visrealm/pico-56/episodes/ep01-vga/ep01-vga-04-boing/res/background.png

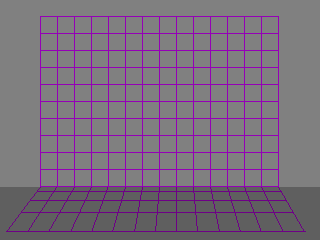
episodes/ep01-vga/ep01-vga-04-boing/res/background.png
