visrealm/pico-56/episodes/ep01-vga/ep01-vga-08b-image-800/res/birds.png

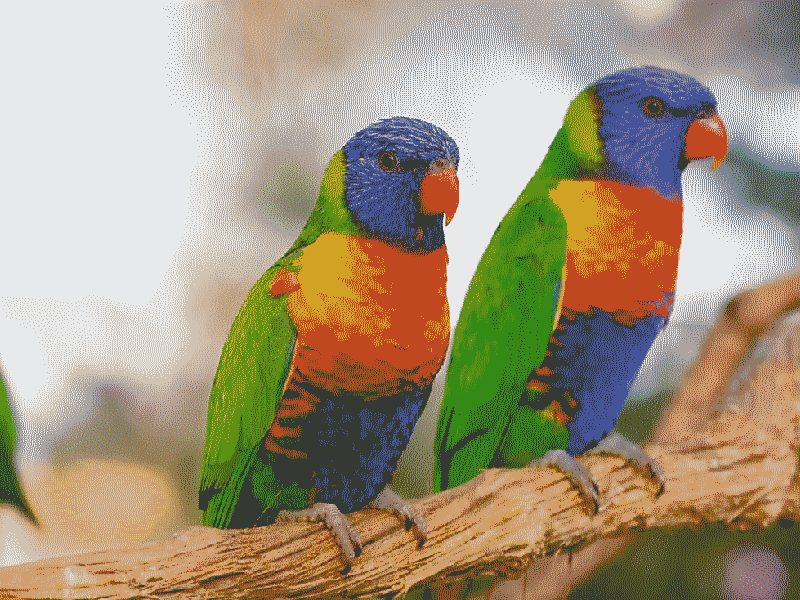
episodes/ep01-vga/ep01-vga-08b-image-800/res/birds.png
