visrealm/pico-56/episodes/ep01-vga/ep01-vga-09-slideshow/res/toucan.png

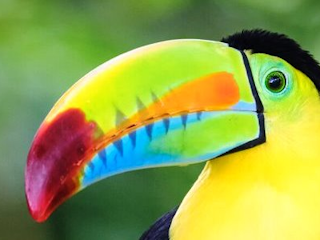
episodes/ep01-vga/ep01-vga-09-slideshow/res/toucan.png
