visrealm/pico-56/img/breadboard_1.jpg

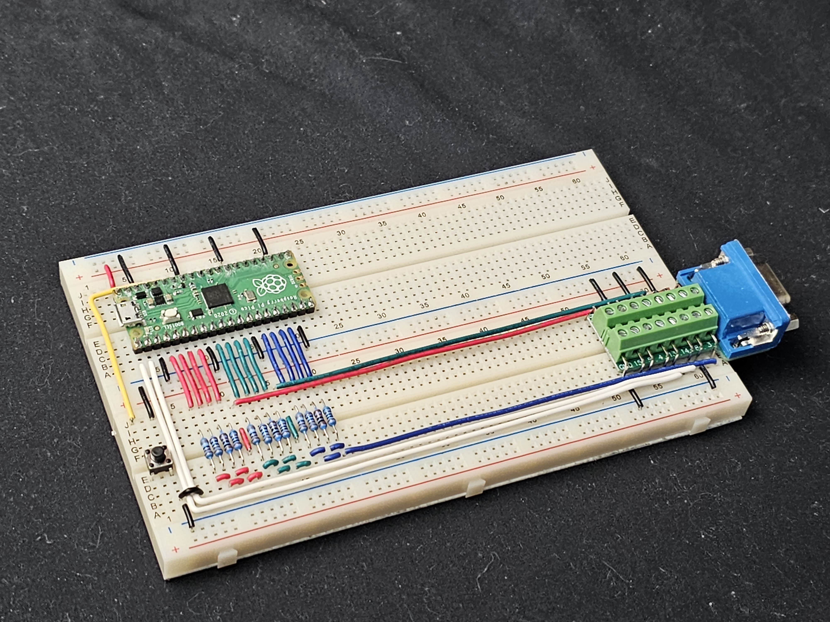
img/breadboard_1.jpg
