visrealm/pico-56/img/image-800-sm.gif

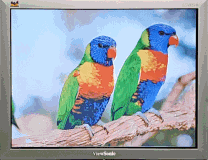
img/image-800-sm.gif
