visrealm/pico-56/img/pcb03.jpg

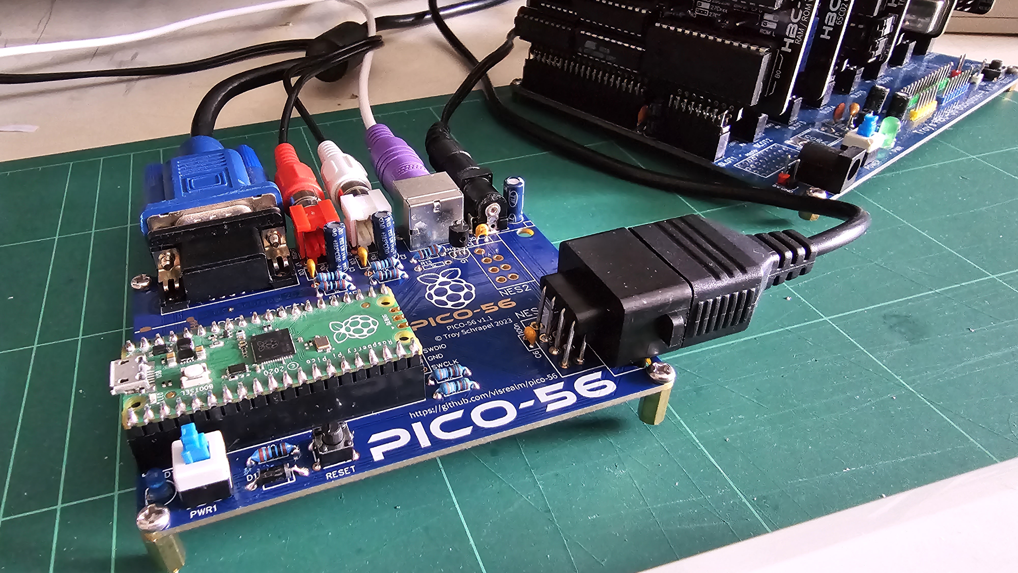
img/pcb03.jpg
