visrealm/pico-56/img/pcb_back_v1_2.png

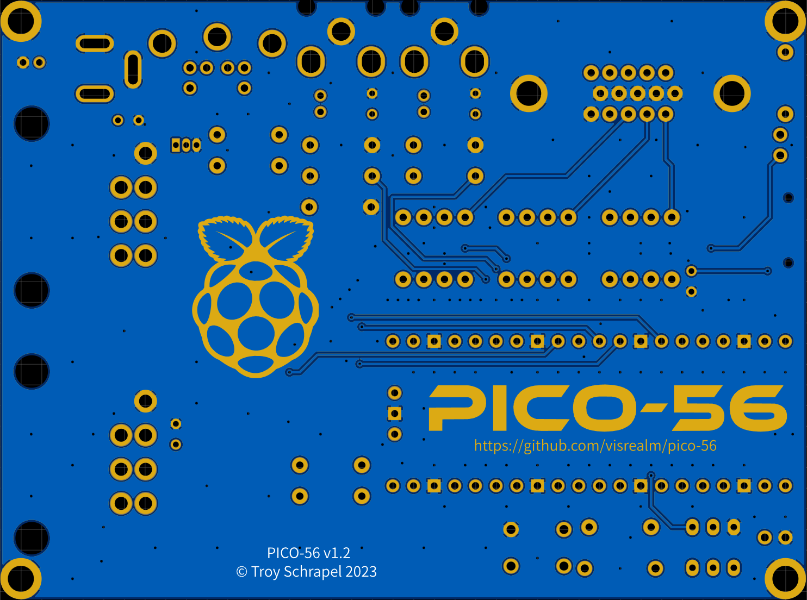
img/pcb_back_v1_2.png
