visrealm/pico-56/img/pcb_front_v1_2.png

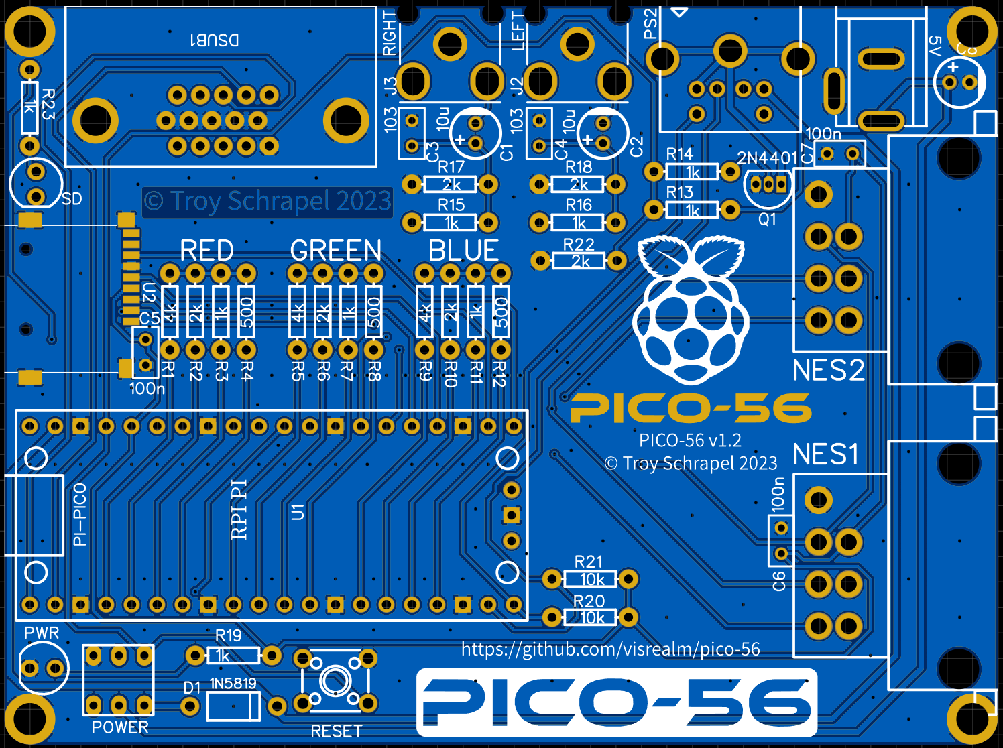
img/pcb_front_v1_2.png
